SelectLOL1/Schulprojekt2020/Dok/bestellungen/digikeybestellung2.png

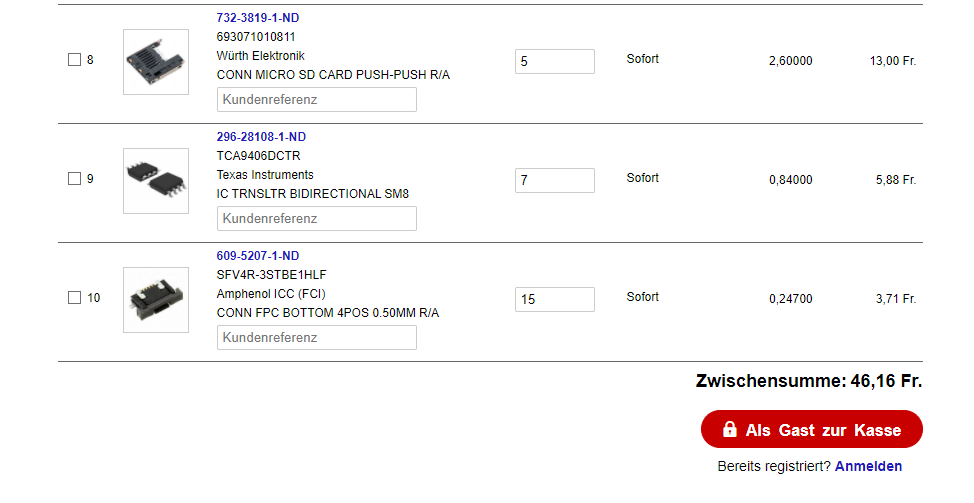
Dok/bestellungen/digikeybestellung2.png
