SelectLOL1/Schulprojekt2020/Dok/bestellungen/digikeybestellung.png

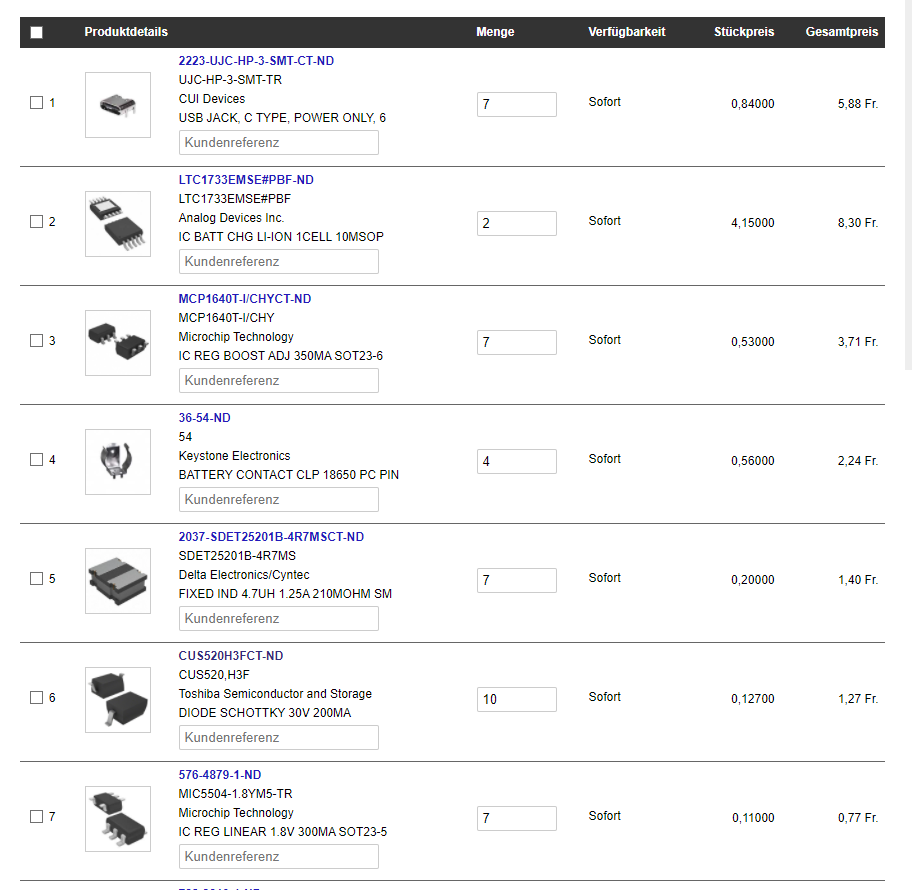
Dok/bestellungen/digikeybestellung.png
