SelectLOL1/Schulprojekt2020/Dok/blockschaltbildairquality2.png

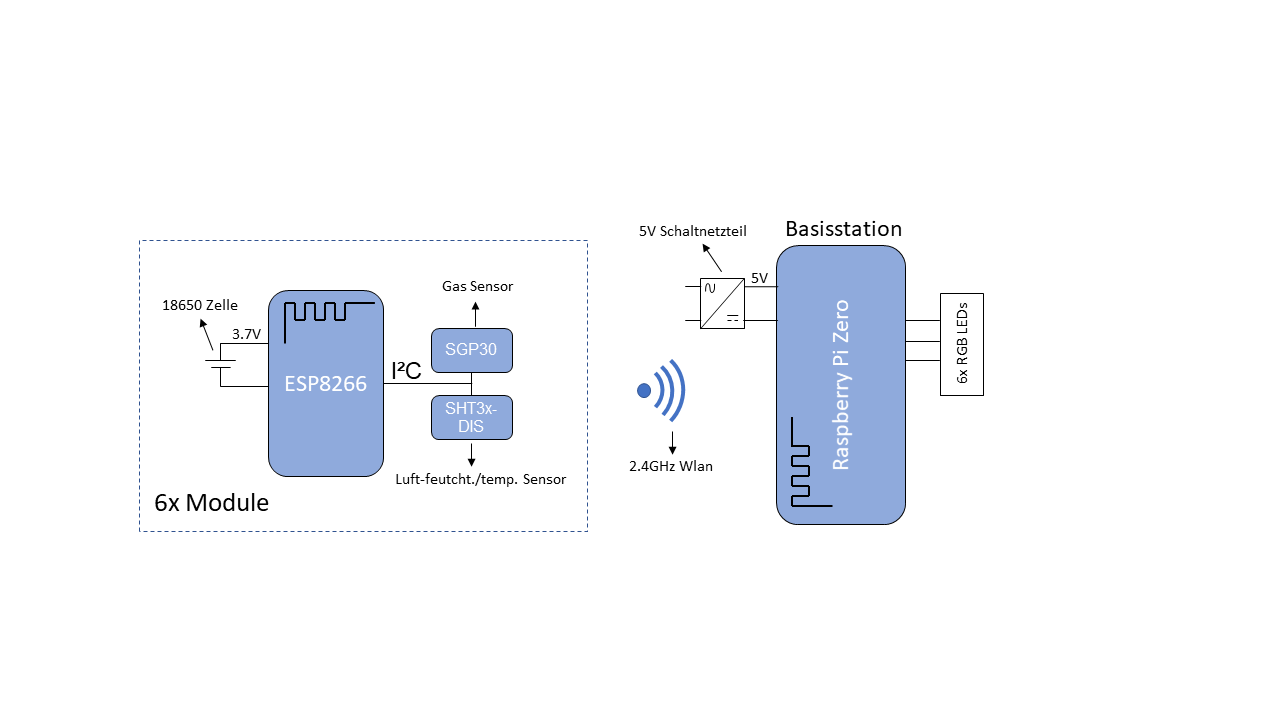
Dok/blockschaltbildairquality2.png
