SelectLOL1/Schulprojekt2020/Dok/Datum.png

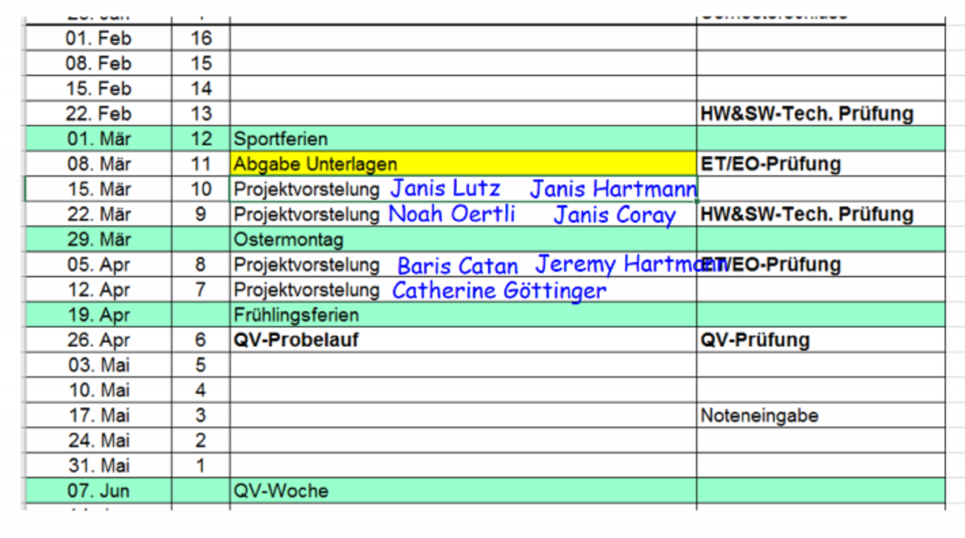
Dok/Datum.png
